RobJansen62/RGB-LED-Strip-Controller/hardware/RGB_LED_Strip_Contoller.kicad_sch

## KiCad design hardware/RGB_LED_Strip_Contoller.kicad_sch (2024-12-21)

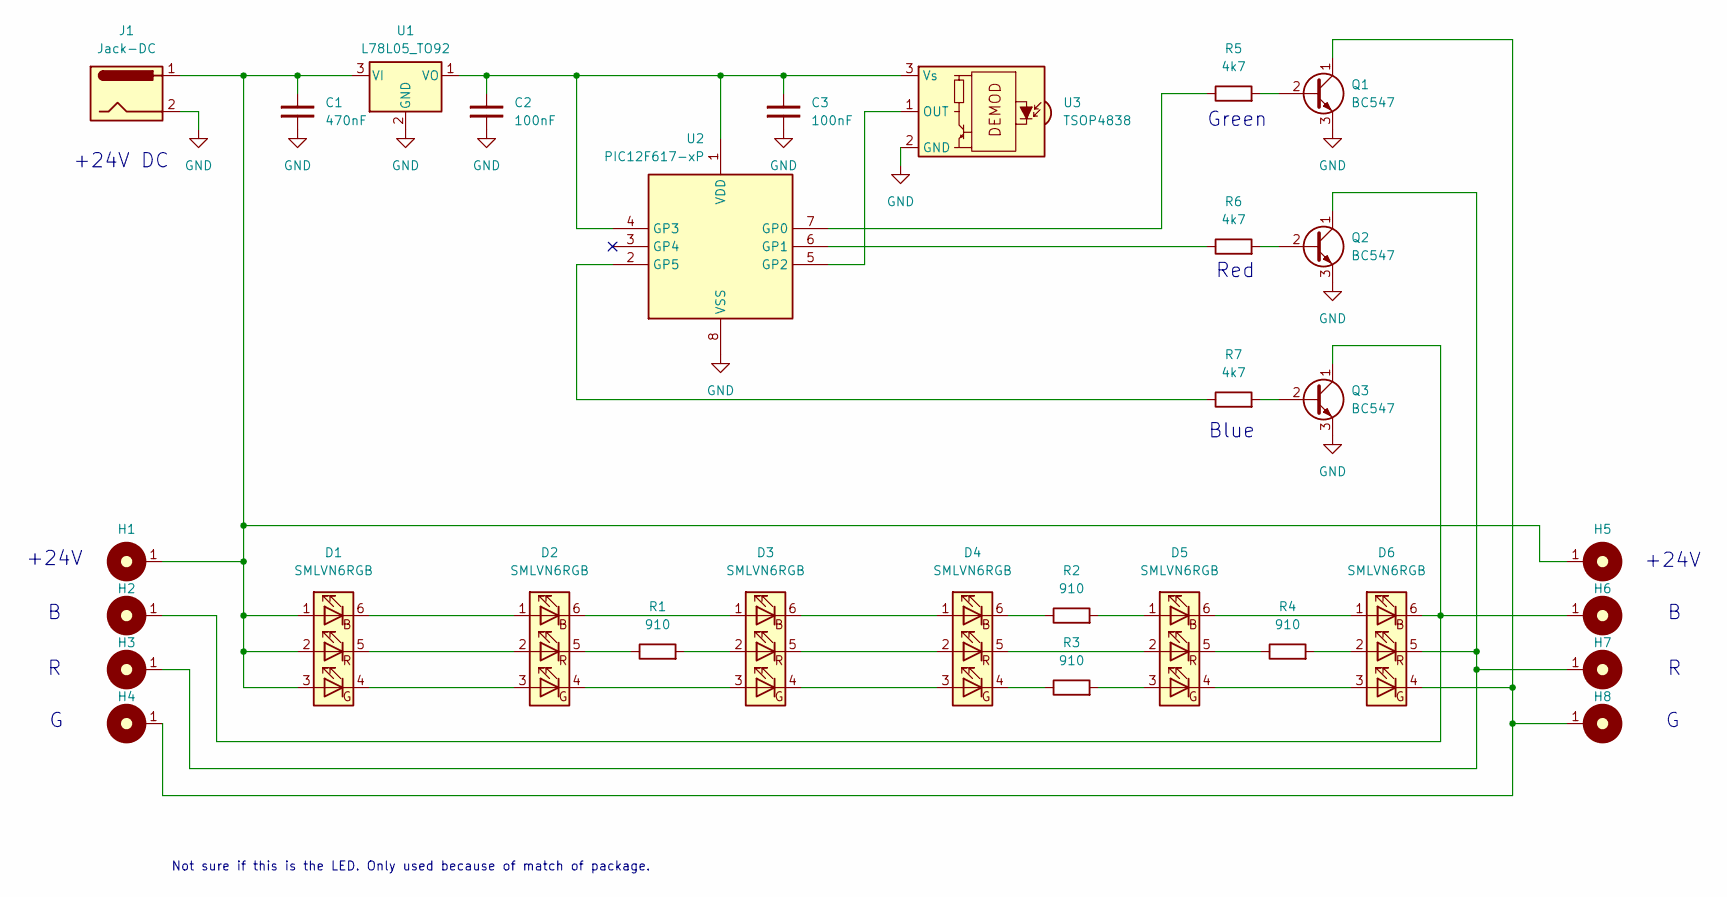
[picture p3: schematic RGB_LED_Strip_Contoller.kicad_sch]

Parts:
C1: 470nF; C_Disc_D3.0mm_W2.0mm_P2.50mm
C2, C3: 100nF; C_Disc_D3.0mm_W2.0mm_P2.50mm
D1, D2, D3, D4, D5, D6: SMLVN6RGB; LED_ROHM_SMLVN6
H1, H2, H3, H4, H5, H6, H7, H8: MountingHole_M3_3.2mm_Pad; MountingHole_3.2mm_Pad
J1: Jack-DC
Q1, Q2, Q3: BC547; TO-92_Inline
R1, R2, R3, R4: 910
R5, R6, R7: 4k7
U1: L78L05_TO92; TO-92_Inline
U2: PIC12F617-xP; DIP-8_W7.62mm
U3: TSOP4838; Vishay_MINICAST-3Pin

Connections:
GND: C1.1, C2.1, C3.1, J1.2, Q1.3 (E), Q2.3 (E), Q3.3 (E), U1.2 (GND), U2.8 (VSS), U3.2 (GND)
unnamed: C1.2, D1.1 (BA), D1.2 (RA), D1.3 (GA), H1.1, H5.1, J1.1, U1.3 (VI)
unnamed: C2.2, C3.2, U1.1 (VO), U2.1 (VDD), U2.4 (GP3), U3.3 (Vs)
unnamed: D1.4 (GK), D2.3 (GA)
unnamed: D1.5 (RK), D2.2 (RA)
unnamed: D1.6 (BK), D2.1 (BA)
unnamed: D2.4 (GK), D3.3 (GA)
unnamed: D2.5 (RK), R1.1
unnamed: D2.6 (BK), D3.1 (BA)
unnamed: D3.2 (RA), R1.2
unnamed: D3.4 (GK), D4.3 (GA)
unnamed: D3.5 (RK), D4.2 (RA)
unnamed: D3.6 (BK), D4.1 (BA)
unnamed: D4.4 (GK), R3.1
unnamed: D4.5 (RK), D5.2 (RA)
unnamed: D4.6 (BK), R2.1
unnamed: D5.1 (BA), R2.2
unnamed: D5.3 (GA), R3.2
unnamed: D5.4 (GK), D6.3 (GA)
unnamed: D5.5 (RK), R4.1
unnamed: D5.6 (BK), D6.1 (BA)
unnamed: D6.2 (RA), R4.2
unnamed: D6.4 (GK), H4.1, H8.1, Q1.1 (C)
unnamed: D6.5 (RK), H3.1, H7.1, Q2.1 (C)
unnamed: D6.6 (BK), H2.1, H6.1, Q3.1 (C)
unnamed: Q1.2 (B), R5.2
unnamed: Q2.2 (B), R6.2
unnamed: Q3.2 (B), R7.2
unnamed: R5.1, U2.7 (GP0)
unnamed: R6.1, U2.6 (GP1)
unnamed: R7.1, U2.2 (GP5)
unnamed: U2.5 (GP2), U3.1 (OUT)

Notes on the sheet:
+24V DC
Not sure if this is the LED. Only used because of match of package.
Red
+24V
Blue
Green
